rileyzilka01/robotic-hand/model/servo-model/SG90 - Micro Servo 9g - Tower Pro.5.SLDPRT

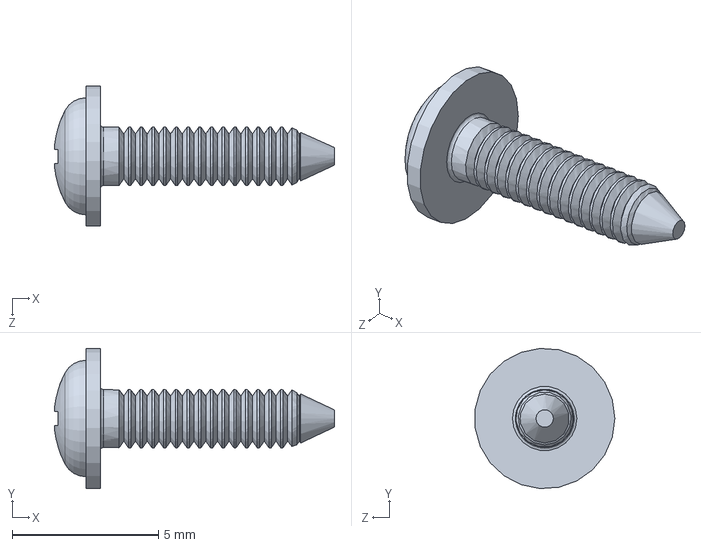
[picture p22: CAD file, 2022-11-21]
model/servo-model/SG90 - Micro Servo 9g - Tower Pro.5.SLDPRT
9.57 x 4.79 x 4.78 mm
