rileyzilka01/robotic-hand/model/hand-parts/finger-tip-bigger-hook.SLDPRT

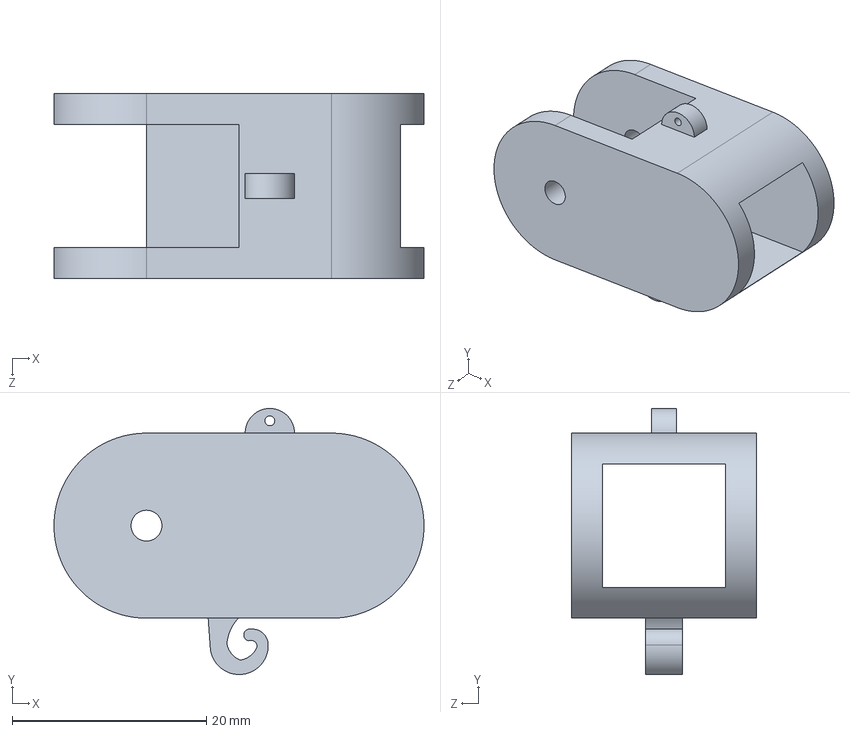
[picture p23: CAD file, 2022-11-28]
model/hand-parts/finger-tip-bigger-hook.SLDPRT
38.1 x 27.4 x 19.1 mm
