rileyzilka01/robotic-hand/model/hand-parts/metal-connector.SLDPRT

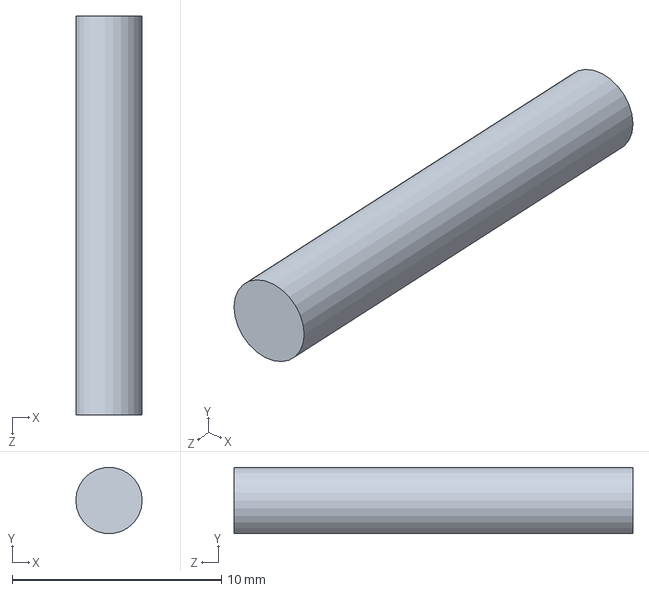
[picture p24: CAD file, 2022-11-22]
model/hand-parts/metal-connector.SLDPRT
3.17 x 3.15 x 19.1 mm
