rileyzilka01/robotic-hand/model/servo-model/SG90 - Micro Servo 9g - Tower Pro.6.SLDPRT

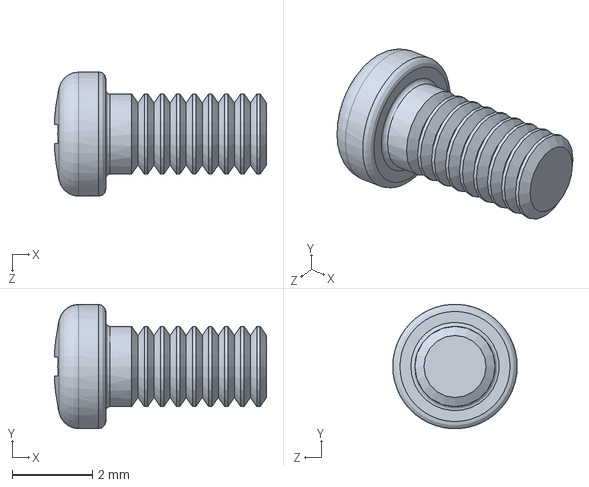
[picture p25: CAD file, 2022-11-21]
model/servo-model/SG90 - Micro Servo 9g - Tower Pro.6.SLDPRT
5.28 x 3.10 x 3.10 mm
