rileyzilka01/robotic-hand/model/servo-model/SG90 - Micro Servo 9g - Tower Pro.2.SLDPRT

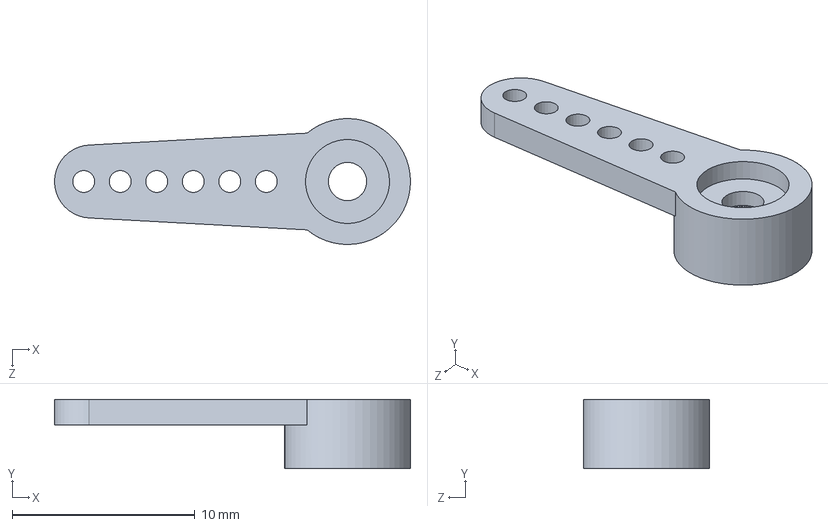
[picture p26: CAD file, 2022-11-21]
model/servo-model/SG90 - Micro Servo 9g - Tower Pro.2.SLDPRT
19.5 x 3.80 x 6.90 mm
