rileyzilka01/robotic-hand/model/servo-model/SG90 - Micro Servo 9g - Tower Pro.4.SLDPRT

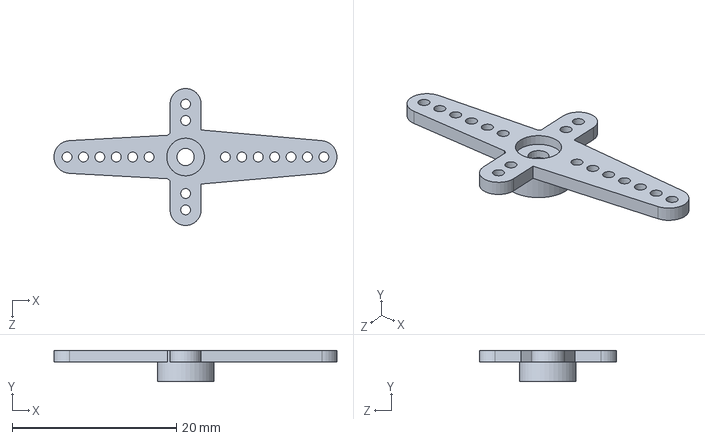
[picture p27: CAD file, 2022-11-21]
model/servo-model/SG90 - Micro Servo 9g - Tower Pro.4.SLDPRT
34.5 x 3.80 x 16.7 mm
